nradulovic/hw_compact/ltspice/pamp/pab3bbb-compact.asc

C1: polcap; 100µ; V=25 Irms=0.44 Rser=0.19 Lser=4.5n Rpar=4110k Cpar=3p
C2: polcap; 1m; V=6.3 Irms=1.44 Rser=0.09 Lser=5.5n Rpar=1110k Cpar=3p
C3: cap; 68p; Rser=970m Lser=5n Rpar=2meg Cpar=1p
C4: polcap; 4m7; V=50 Irms=2.5 Rser=0.055 Lser=20n Rpar=40k Cpar=3p
C5: cap; 100n; Rser=700m Lser=7n Rpar=4.4meg Cpar=1p
C6: cap; 470n; Rser=700m Lser=7n Rpar=4.4meg Cpar=1p
C7: polcap; 470µ; V=25 Irms=1.44 Rser=0.19 Lser=4.5n Rpar=1810k Cpar=2p
C8: cap; 100n; Rser=700m Lser=7n Rpar=4.4meg Cpar=1p
C9: cap; 2n7; Rser=970m Lser=5n Rpar=2meg Cpar=1p
C11: polcap; 470µ; V=50 Irms=2.5 Rser=0.055 Lser=20n Rpar=40k Cpar=3p
C12: polcap; 4m7; V=50 Irms=2.5 Rser=0.055 Lser=20n Rpar=40k Cpar=3p
C13: polcap; 100µ; V=25 Irms=0.44 Rser=0.19 Lser=4.5n Rpar=4110k Cpar=3p
C14: polcap; 2m2; V=50 Irms=2.5 Rser=0.055 Lser=20n Rpar=40k Cpar=3p
C15: polcap; 2m2; V=50 Irms=2.5 Rser=0.055 Lser=20n Rpar=40k Cpar=3p
C23: cap; 470n; Rser=700m Lser=7n Rpar=4.4meg Cpar=1p
C24: cap; 100n; Rser=700m Lser=7n Rpar=4.4meg Cpar=1p
D1: schottky; MBR20100CT
D2: schottky; MBR20100CT
D4: diode; 1N4148
D5: diode; BAV21
D6: schottky; GBPC3502
D7: diode; BAV21
D8: diode; 1N4148
D9: schottky; GBPC3502
D10: schottky; GBPC3502
D11: schottky; GBPC3502
Ii: current; 0; AC {u(prb)}
L1: ind; {Zimg}
L2: ind; 200n; Rser=0.22 Rpar=100meg Cpar=1p
L3: ind; 200n; Rser=0.22 Rpar=100meg Cpar=1p
L4: ind; 4n; Rser=1m
L5: ind; 100n; Rser=20m
L6: ind; 50n; Rser=20m
L7: ind; 100n; Rser=20m
L8: ind; 100n; Rser=20m
L9: ind; 50n; Rser=20m
L10: ind; 20n; Rser=10m
L11: ind; 20n; Rser=10m
LPWRGND: ind2; {con1_len*7n}; Rser={con1_len*.5m}
LSPKN2: ind2; {con2_len*7n}; Rser={con2_len*.5m}
LSPKP: ind2; {con2_len*7n}; Rser={con2_len*.5m}
LTRF: ind2; 4µ; Rser=10m Rpar=3meg Cpar=1p
LVCC: ind2; {con1_len*7n}; Rser={con1_len*.5m}
LVEE: ind2; {con1_len*27n}; Rser={con1_len*.5m}
PBIAS1: res; {1+(500*BIAS)}
PBIAS2: res; {1+(1k*LTPBIAS)}
Q1: pnp; CA_BC560C
Q2: npn; 2SC3503F
Q3: pnp; CA_BC560C
Q4: npn; MJE340
Q5: pnp; 2SA1381F
Q6: pnp; 2SA1381F
Q7: pnp; MJL1302A
Q8: npn; CA_MJE243
Q9: npn; MJL3281A
Q10: pnp; CA_MJE253
Q11: pnp; 2SA1381F
Q12: npn; 2N5550
R1: res; 10k
R2: res; {nfb1}
R3: res; {nfb2}
R4: res; .47
R5: res; 39
R6: res; 33
R7: res; 680
R8: res; 200
R9: res; {Zreal}
R10: res; 10k
R11: res; 240
R12: res; {nfb1}
R13: res; 20
R14: res; 680
R15: res; 33
R16: res; 100
R17: res; 100
R18: res; 25m
R19: res; 4.7
R20: res; {nfb2}
R21: res; 3k
R22: res; 200
R23: res; 20
R24: res; 3.3
R25: res; 3.3
R26: res; 100
R27: res; 3.3
R28: res; 15m
R30: res; 33
R31: res; 3k
R32: res; 200
R33: res; 300
R34: res; 10
R35: res; 3.3
R37: res; 33
R38: res; 25m
R41: res; 15m
R43: res; 15m
R45: res; .47
R46: res; 10k
R49: res; 10
R54: res; 10
V1: voltage; 0
V2: voltage; SINE(0 {supplyVLT*sqrt(2)} 50 1m 0 {phi}); Rser={rser}
V3: voltage; SINE(0 {supplyVLT*sqrt(2)} 50 1m 0 {phi}); Rser={rser}
V4: voltage; 0
V5: voltage; SINE(0 {vinput/3} 60 0 0)
V6: voltage; 0
V7: voltage; PULSE(0 {vinput} 1u 1n 1n {1/(freq*2)} {1/freq})
V8: voltage; PULSE(0 {-vinput} {1u+(1/(freq*2))} 1n 1n {1/(freq*2)} {1/freq})
V9: voltage; SINE(0 {vinput/3} 19k)
V10: voltage; SINE(0 {vinput/3} 20k 0 0)
V11: voltage; SINE(0 {vinput} {freq} 10m 10 0 5)
V14: voltage; SINE(0 {vinput} {freq} 310m 10 0 5)
V15: voltage; SINE(0 {vinput} {freq} 0 0 0 0)
V18: voltage; 0
Vi: voltage; 0; AC {u(-prb)}
Named nets: x, xp, pwrgnd, sgnd, intermet, vcc, vee, speaker, impulse, AC1, AC2, SPK+, SPK-, imd, 0, sinus, out_i, spkgnd, lngnd
.op
.option plotwinsize=0
.option noopiter
Transient
.four {freq} 10 {iterations} v(SPK+,SPK-)
.param prb=0
.param timestep={1/((65536/8)*freq)}
.param freq=600
.param stoptime {iterations/freq}
.ac oct 100 10 100meg
.step param prb list -1 1
AC analysis
.param iterations=100
.param Zimp=8
.param Zreal Zimp/2
.param Zimg (Zimp*sqrt(3))/(4*pi*freq)
.param supplyPWR=40
.param supplyVLT={18}
.param voutput=16
.param supplyK 0.06
.param rser {(supplyVLT*supplyVLT*supplyK)/(2*supplyPWR)}
.tran 0 {stoptime} 100n {timestep}
.param phi=90
.param con1_len=5
.param con2_len 10
KCON2 LSPKP LSPKN2 0.8
Konektor zvucnika i zvucnik
Konektor napajanja, star ground i napajanje
Ulazni parametri kola
AC sonda
.lib ../spice_root/lib/FCS_D.lib
.param BIAS=0.48
.param vinput voutput*(nfb1/nfb2)
.param nfb1=200
.param nfb2=3k
1W
1W
4 ohm, 10 cycles, 90W
8 ohm, 10 cycles, 50W
.step temp 0 60 20
5W
5W
.lib ../spice_root/lib/ONNN_BJT.lib
.lib ../spice_root/lib/STM_D.lib
.lib ../spice_root/lib/FCS_BJT.lib
.lib ../spice_root/lib/ONNN_D.lib
.lib ../spice_root/lib/TSE_BJT.lib
.lib ../spice_root/lib/VSH_FET.lib
.param LTPBIAS=0.48
