nradulovic/hw_compact/ltspice/pamp/pab3bbb-compact-module.asc

C1: cap; 47µ; Rser=220m Lser=5n Rpar=800k Cpar=1p
C2: cap; 470µ; Rser=112m Lser=5n Rpar=600k Cpar=1p
C3: cap; 100p; Rser=970m Lser=5n Rpar=2meg Cpar=1p
C4: cap; 10n; Rser=970m Lser=5n Rpar=2meg Cpar=1p
D2: diode; BAV21
D6: diode; BAV21
D9: diode; BAV21
D10: diode; BAV21
L2: ind; 15n; Rser=20m
L3: ind; 15n; Rser=20m
L9: ind; 10n; Rser=10m
L10: ind; 10n; Rser=10m
L12: ind; 10n; Rser=10m
PBIAS1: res; {1+(500*BIAS)}
Q1: npn; CA_NJL3281
Q2: npn; CA_MJE15032C
Q3: npn; 2SC3503F
Q4: npn; 2SC3503F
Q5: pnp; CA_NJL1302
Q6: pnp; 2SA1381F
Q7: pnp; CA_BC560C
Q8: pnp; CA_BC560C
Q9: pnp; 2SA1381F
Q10: pnp; 2SA1381F
Q11: pnp; CA_BC560C
Q14: pnp; CA_MJE15033C
Q21: npn; MJE340
R1: res; 750
R2: res; 3k
R3: res; 100
R4: res; 100
R5: res; 22
R6: res; 27
R7: res; 750
R8: res; 3k
R9: res; 1k5
R10: res; 51
R11: res; 10
R12: res; 2.4
R13: res; 10
R14: res; 0.22
R16: res; 51
R17: res; 150
R18: res; 100
R19: res; 24
R20: res; 2.4
R21: res; 0.22
R27: res; 24
R37: res; 300
R52: res; 1k5
Named nets: pvcc, pvee, out, ninv, inv, pvcc_i, out_i, 0
5W
5W
.lib ../spice_root/lib/ONNN_BJT.lib
.lib ../spice_root/lib/STM_D.lib
.lib ../spice_root/lib/FCS_BJT.lib
.lib ../spice_root/lib/ONNN_D.lib
.lib ../spice_root/lib/TSE_BJT.lib
.lib ../spice_root/lib/VSH_FET.lib
