nradulovic/hw_compact/ltspice/pamp/pab3bbb-sewa.asc

C1: polcap; 22µ; V=6.3 Irms=1.44 Rser=0.09 Lser=5.5n Rpar=1110k Cpar=3p
C2: polcap; 22µ; V=6.3 Irms=1.44 Rser=0.09 Lser=5.5n Rpar=1110k Cpar=3p
C3: polcap; 100µ; V=6.3 Irms=1.44 Rser=0.09 Lser=5.5n Rpar=1110k Cpar=3p
C4: cap; 100n; Rser=700m Lser=7n Rpar=4.4meg Cpar=1p
C5: cap; 18p
C6: polcap; 2m2; V=50 Irms=2.5 Rser=0.085 Lser=20n Rpar=40k Cpar=3p
C8: cap; 100n; Rser=700m Lser=7n Rpar=4.4meg Cpar=1p
C9: cap; 2n2
C11: cap; 100n
C13: polcap; 100µ; V=6.3 Irms=1.44 Rser=0.09 Lser=5.5n Rpar=1110k Cpar=3p
C23: cap; 470n; Rser=700m Lser=7n Rpar=4.4meg Cpar=1p
C24: cap; 100n; Rser=700m Lser=7n Rpar=4.4meg Cpar=1p
C32: polcap; 220µ; V=63 Irms=2.77 Rser=0.070 Lser=4n Rpar=1900k Cpar=3p
D9: schottky; GBPC3502
Ii: current; 0; AC {u(prb)}
L1: ind; {Zimg}
L4: ind; 4n; Rser=1m
L6: ind; 4n; Rser=1m
LGSPK1: ind2; {con2_len*17n}; Rser={con2_len*.5m}
LGSPK2: ind2; {con1_len*17n}; Rser={con1_len*.5m}
LPWRGND: ind2; {con1_len*7n}; Rser={con1_len*.5m}
LSPKN2: ind2; {con2_len*7n}; Rser={con2_len*.5m}
LSPKP: ind2; {con2_len*7n}; Rser={con2_len*.5m}
LTRF: ind2; 2µ; Rser=10m Rpar=3meg Cpar=1p
LVCC: ind2; {con1_len*7n}; Rser={con1_len*.5m}
LVEE: ind2; {con1_len*27n}; Rser={con1_len*.5m}
R2: res; {nfb1}
R3: res; {nfb2}
R4: res; 10
R9: res; {Zreal}
R10: res; 10k
R12: res; {nfb1}
R18: res; 25m
R19: res; 2.2
R20: res; {nfb2}
R26: res; 25m
R28: res; 15m
R38: res; 25m
R40: res; 10
R41: res; 15m
R43: res; 15m
R45: res; .47
R46: res; 10k
R49: res; 10
R54: res; 10
V1: voltage; 0
V3: voltage; SINE(0 {supplyVLT} 50 1m 0 {phi}); Rser={rser}
V4: voltage; 0
V5: voltage; SINE(0 {vinput/3} 60 0 0)
V6: voltage; 0
V7: voltage; PULSE(0 {vinput} 1u 1n 1n {1/(freq*2)} {1/freq})
V8: voltage; PULSE(0 {-vinput} {1u+(1/(freq*2))} 1n 1n {1/(freq*2)} {1/freq})
V9: voltage; SINE(0 {vinput/3} 19k)
V10: voltage; SINE(0 {vinput/3} 20k 0 0)
V11: voltage; SINE(0 {vinput} {freq} 10m 10 0 5)
V14: voltage; SINE(0 {vinput} {freq} 310m 10 0 5)
V15: voltage; SINE(0 {vinput} {freq} 0 0 0 0)
V18: voltage; 0
Vi: voltage; 0; AC {u(-prb)}
X1: pab3bbb-sewa-module
Named nets: x, out, xp, pwrgnd, sgnd, intermet, vcc, vee, gspk, speaker, impulse, AC1, AC2, SPK+, SPK-, imd, 0, sinus
.op
.option plotwinsize=0
.option noopiter
Transient
.four {freq} 10 10 v(SPK+,SPK-)
.param prb=0
.param timestep={1/((65536/8)*freq)}
.param freq=1k
.param stoptime {iterations/freq}
.ac oct 100 10 100meg
.step param prb list -1 1
AC analysis
.param iterations=80
.param Zimp=8
.param Zreal Zimp/2
.param Zimg (Zimp*sqrt(3))/(4*pi*freq)
.param supplyPWR=40
.param supplyVLT=20
.param voutput=6
.param supplyK 0.06
.param rser {(supplyVLT*supplyVLT*supplyK)/(2*supplyPWR)}
.tran 0 {stoptime} 100n {timestep}
.param phi=90
.param con1_len=5
.param con2_len 100
KCON2 LSPKP LSPKN2 0.8
Konektor zvucnika i zvucnik
Konektor napajanja, star ground i napajanje
Ulazni parametri kola
AC sonda
.lib ../spice_root/lib/FCS_D.lib
.param BIAS=0.38
.param vinput voutput*(nfb1/nfb2)
.param nfb1=100
.param nfb2=1k8
0.5W
1W
.step temp 0 60 20
