nradulovic/hw_compact/ltspice/pamp/pab3bbb-arguo-prot-2slope.asc

D1: diode; BAV21
D2: schottky; BAT46WJ
I1: current; 12.2m
Q16: npn; BC546B
Qpdh: npn; CA_MJE15032C
Qph1: npn; CA_NJL3281
R1: res; {62/2}
R5: res; 2.2
R9: res; 27k
R12: res; 750
R13: res; 330
R14: res; 0.22
R27: res; 24
V1: voltage; PULSE(2 100 2m 98m 1m)
Named nets: pvcc, 0
.lib ../spice_root/lib/ONNN_BJT.lib
.lib ../spice_root/lib/STM_D.lib
.lib ../spice_root/lib/FCS_BJT.lib
.lib ../spice_root/lib/FCS_D.lib
.lib ../spice_root/lib/ONNN_D.lib
.lib ../spice_root/lib/TSE_BJT.lib
.lib ../spice_root/lib/TXN_IC.lib
.tran 100ms
.param rs={910/2}
