nradulovic/hw_compact/ltspice/pamp/pab3bbb-compact-ops.asc

L9: ind; 10n; Rser=10m
L12: ind; 10n; Rser=10m
M1: nmos; CA_IRFP240C
M2: nmos; CA_IRFP240C
Qpdh: npn; CA_MJE15032C
Qpdl: pnp; CA_MJE15033C
R1: res; 43
R2: res; 4
R5: res; 100
R12: res; 10
R13: res; 43
R14: res; 0.22
R21: res; 0.22
R27: res; 22
R30: res; 22
R68: res; 100
V1: voltage; 24
V2: voltage; 24
V3: voltage; {vbias/2}
V4: voltage; SINE(1.6 17 10 1u); AC 1
V5: voltage; {vbias/2}
Named nets: pvcc, pvee, 0, out, in
.lib ..//spice_root/lib/ONNN_BJT.lib
.lib ../spice_root/lib/STM_D.lib
.lib ..//spice_root/lib/FCS_BJT.lib
.lib ../spice_root/lib/FCS_D.lib
.lib ../spice_root/lib/ONNN_D.lib
.lib ../spice_root/lib/TSE_BJT.lib
.step oct param ibase 0.1m 2m 20
;op
.param vbias=6.7
.tran 0 0.099 1m
.ac oct 10 100 50meg
.lib ../spice_root/lib/VSH_FET.lib
