nradulovic/hw_compact/ltspice/pamp/pab3bbb-compact-vbe.asc

I1: current; {ics}
PBIAS1: res; {1+(500*BIAS)}
Q21: npn; MJE340
R37: res; 120
R52: res; 1k
R53: res; 33
Named nets: 0, vbe
.lib ..//spice_root/lib/ONNN_BJT.lib
.lib ../spice_root/lib/STM_D.lib
.lib ..//spice_root/lib/FCS_BJT.lib
.lib ../spice_root/lib/FCS_D.lib
.lib ../spice_root/lib/ONNN_D.lib
.lib ../spice_root/lib/TSE_BJT.lib
.param ics 12m
.op
.param bias 0.45
.step param ics 4m 20m .5m
